Noor6767/Noor-s-Cat-Pad/Assets/img1.png

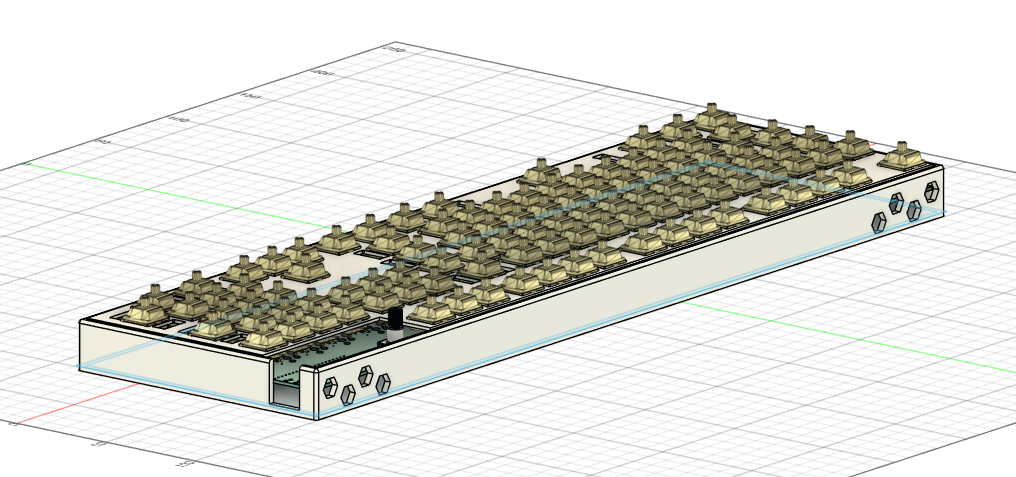
Assets/img1.png
