Noor6767/Noor-s-Cat-Pad/Assets/img2.png

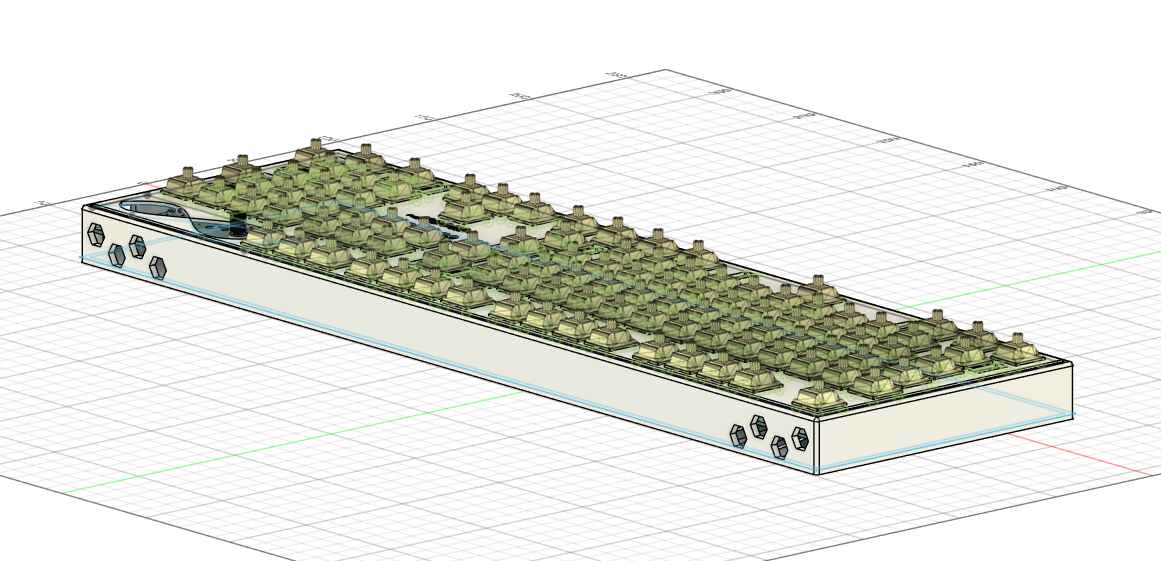
Assets/img2.png
